heatseeknyc/hardware/cell/v0.1-stacked.png

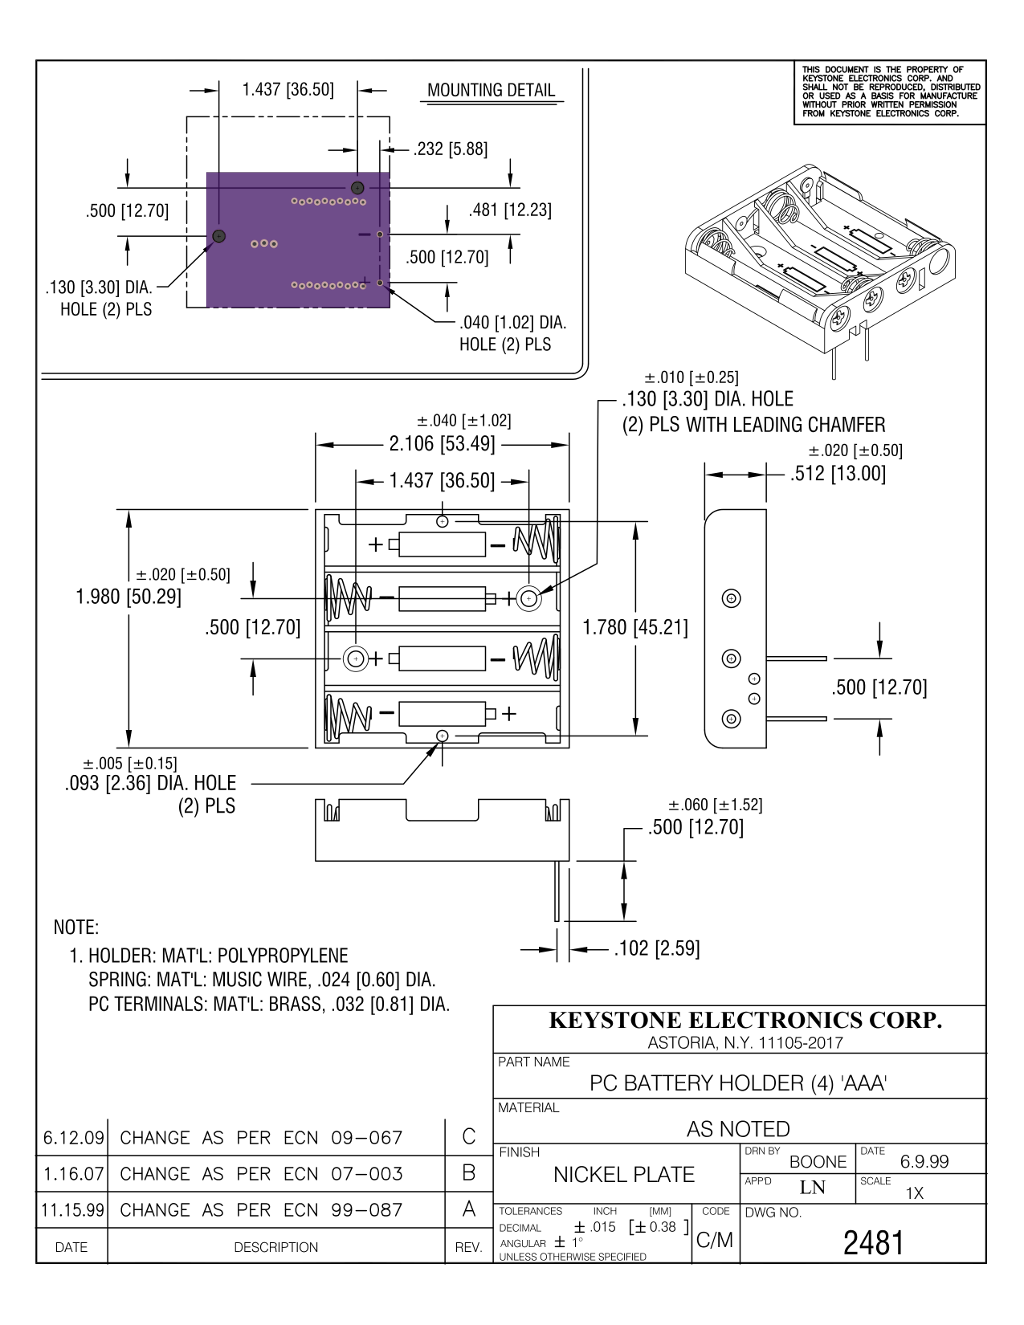
cell/v0.1-stacked.png
