heatseeknyc/hardware/cell/v0.1.png

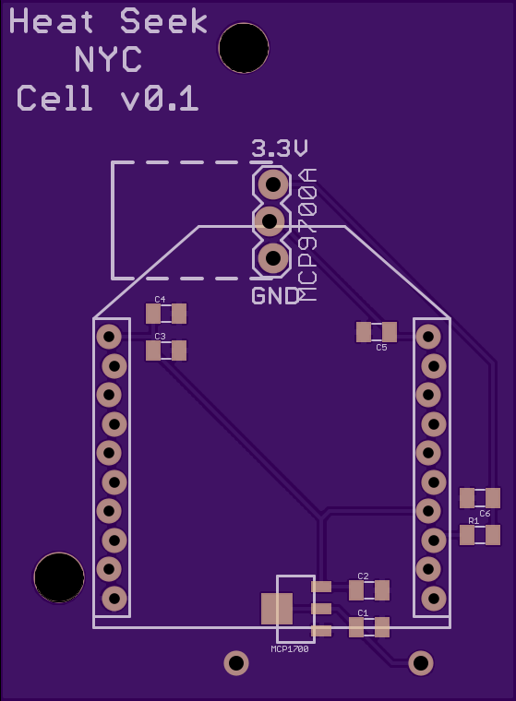
cell/v0.1.png
