heatseeknyc/hardware/hub/stacked/v0.1-bottom.png

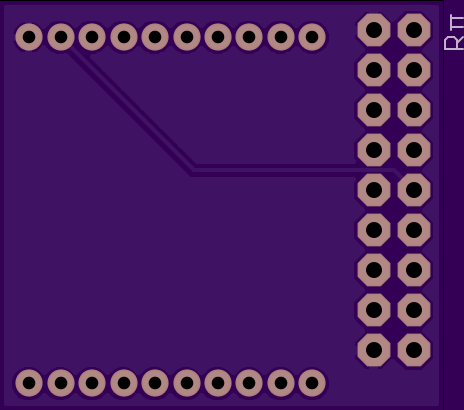
hub/stacked/v0.1-bottom.png
